alexeystn/tiny-blackbox/Python/blackbox_dump.py

import serial
import serial.tools.list_ports
import time
from datetime import datetime
import json
import sys


def load_config():

    with open('config.json', 'r') as f:
        config = json.load(f)
    port = config['port']
    
    port_list = [c.device for c in serial.tools.list_ports.comports()]

    if not port in port_list:
        print('Cannot find serial port \'{0}\''.format(port))
        print('Select one of the availible ports:')
        for i, p in enumerate(port_list):
            print('{0}: {1}'.format(i+1, p))
        n = int(input())
        config['port'] = port_list[n-1]

    return config


def save_config(config):

    with open('config.json', 'w') as f:
        json.dump(config, f, indent=2)  


def check_header(header):

    if header[0:4] == b'\xdd\xcc\xbb\xaa':
        v = int.from_bytes(header[4:8], 'little')
        print()
        print('Flash memory: {0:.1f}% full'.format(v/10))
        print()
    else:
        print('Incorrect device header')
        print()


def bf_enable_passthrough(ser, config):
    
    print()
    print('===== Betafligh CLI mode =====')
            
    ser.write(b'#\n')
    res = ser.readline()

    request_str = 'serialpassthrough ' + str(config['bf_uart_number'] - 1) + ' ' + str(config['baudrate']) + '\n'

    ser.write(request_str.encode())
    while (1):
        res = ser.readline()
        if len(res) == 0:
            break
        s = res.decode().strip()
        if (len(s) > 0):
            print(' >> ' + s)
            
    print('==============================')
    print()


def save_rx_data_to_file(ser, f):
    
    rx_counter = 0
    rx_counter_scaled = 0
    rx_counter_scaled_prev = 0

    try:
        while True: # print dots and megabytes
            d = ser.read(1000)
            if len(d) > 0:
                rx_counter += len(d)
                f.write(d)
                rx_counter_scaled = rx_counter // (2**16)
                if (rx_counter_scaled > rx_counter_scaled_prev):
                    print('.', end='')
                    f.flush()
                    if (rx_counter_scaled % 16 == 0):
                        print(' {0:.0f} Mb'.format(rx_counter/(2**20)))
                rx_counter_scaled_prev = rx_counter_scaled
                
            else:
                break
    except KeyboardInterrupt:
        print()
        print('cancelled')

    print('\n'+str(rx_counter) + ' bytes recieved')
    print(filename + ' saved')    



config = load_config()
    
filename = 'Blackbox_Log_' + datetime.now().strftime('%Y%m%d_%H%M%S.bbl')
f = open(filename, 'wb')

result = 0

with serial.Serial(config['port'], config['baudrate'], timeout=1) as ser:

    result = 1
    print('Open ' + config['port'] + ' successfully')

    if config['use_passthrough'] != 0:
        bf_enable_passthrough(ser, config)

    print('Hold button for 2 seconds', end='')
    
    wait_counter = 0
    while wait_counter < 60:
        print('.', end='')
        h = ser.read(8)
        wait_counter += 1
        if len(h) > 0:
            print()
            check_header(h)               
            break
  
    if len(h) == 0:      
        print()
        print('Serial port timeout')
    else:
        print('Downloading:      Press ctrl+c to stop')
        save_rx_data_to_file(ser, f)

    
if result == 0:
    print('Cannot open ' + port)
else:
    save_config(config)
    
